jaebin401/TILT/CAD/images/calf-foot.png

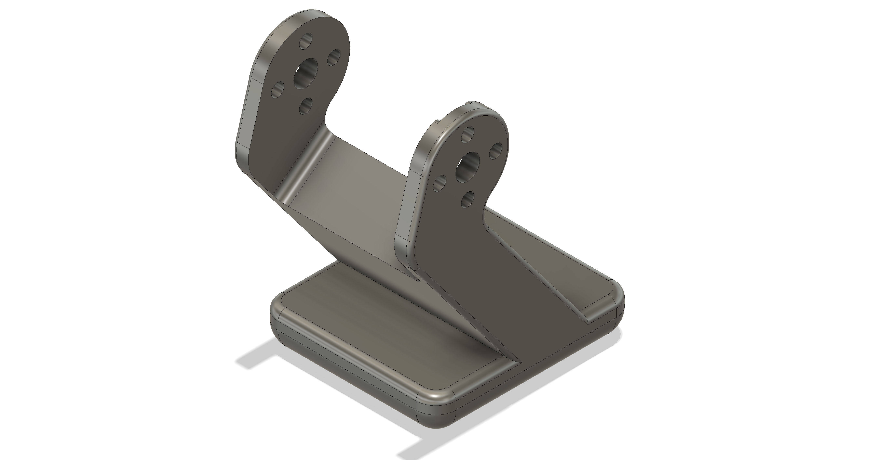
CAD/images/calf-foot.png
