jaebin401/TILT/CAD/images/STS3215.png

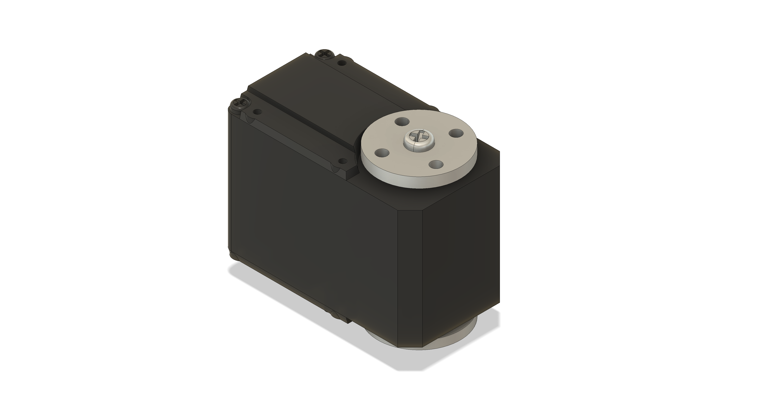
CAD/images/STS3215.png
