jaebin401/TILT/CAD/images/thigh mount.png

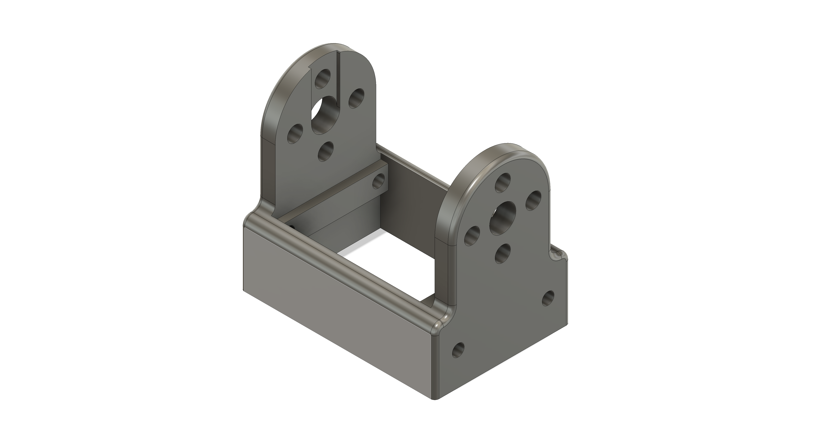
CAD/images/thigh mount.png
