jaebin401/TILT/CAD/images/torso.png

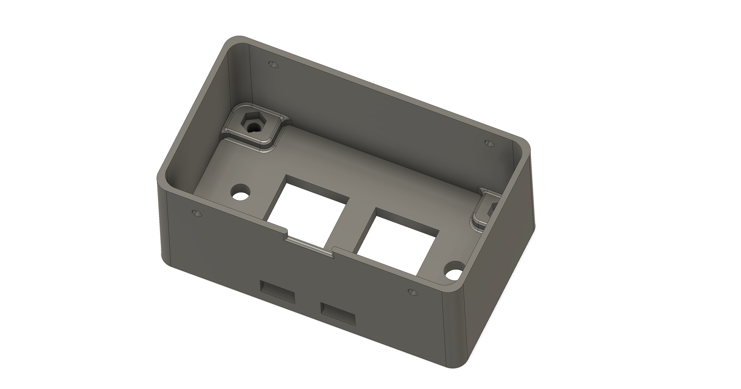
CAD/images/torso.png
